glowfly/glowfly_station/img/cover.jpg

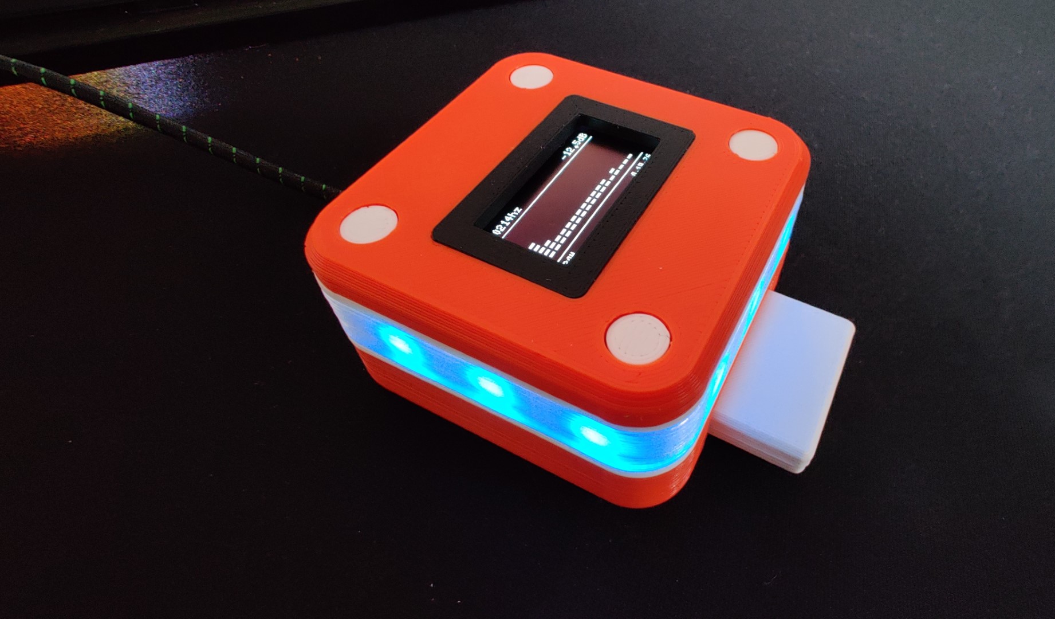
img/cover.jpg
