glowfly/glowfly_station/img/mod-connector.jpg

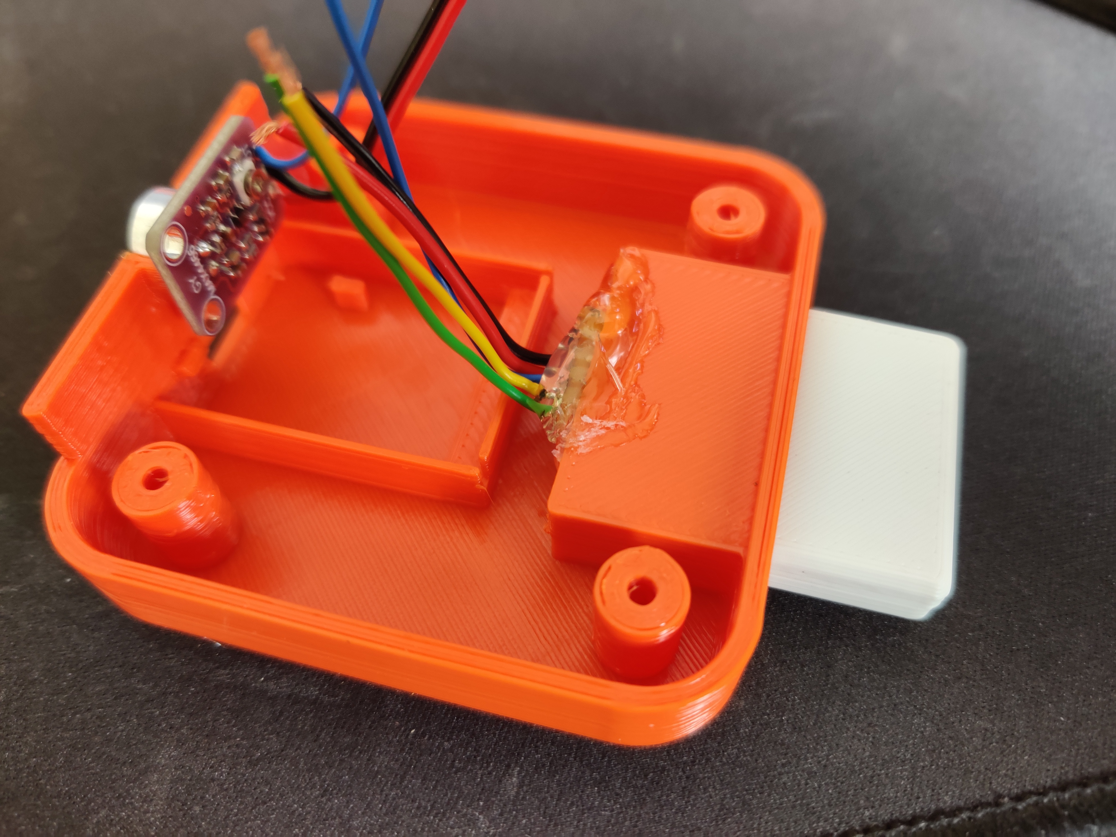
img/mod-connector.jpg
