glowfly/glowfly_station/src/firmware/src/mod/mod.hpp

#ifndef MOD_H
#define MOD_H

#include <string>

namespace SyncBlink
{
    class Mod
    {
        public:
            bool Exists;
            std::string Name;
            std::string Content;
    };
}

#endif // MOD_H
