glowfly/glowfly_station/src/firmware/src/station_context.hpp

#ifndef STATIONCONTEXT_H
#define STATIONCONTEXT_H

#include <memory>
#include <led/led.hpp>
#include <network/websocket/socket_server.hpp>

#include "states/state.hpp"
#include "display/display.hpp"
#include "web/syncblink_web.hpp"
#include "wifi/station_wifi.hpp"
#include "mod/mod_manager.hpp"

namespace SyncBlink
{
    class StationContext
    {
        public:
            StationContext();

            void setup();
            void loop();
            void resetState();

            LED& getLed();
            Display& getDisplay();
            uint32_t getMeshLedCount();
            ModManager& getModManager();
            SocketServer& getSocketServer();

            std::shared_ptr<State> currentState;

        private:
            void startMeshCount();
            void onSocketServerMeshConnection();
            void onSocketServerCommandReceived(Server::Command command);

            LED _led;
            Display _display;
            StationWifi _wifi;
            ModManager _modManager;
            SocketServer _socketServer;
            
            SyncBlinkWeb _web;

            uint32_t _meshLedCount = LED_COUNT;
    };
}

#endif // STATIONCONTEXT_H
