glowfly/glowfly_station/src/firmware/src/wifi/station_wifi.hpp

#ifndef STATIONWIFI_H
#define STATIONWIFI_H

#include <string>
#include <network/mesh/syncblink_mesh.hpp>

namespace SyncBlink
{
    class StationWifi
    {
        public:
            StationWifi();

            void connectWifi();
            void saveWifi(std::string ssid, std::string pass);

            std::string getSavedSSID();
            std::string getSavedPass();

        private:
            SyncBlinkMesh _mesh;
    };
}

#endif // STATIONWIFI_H
